seko99/robot/docs/2025-05-10_15-37.png

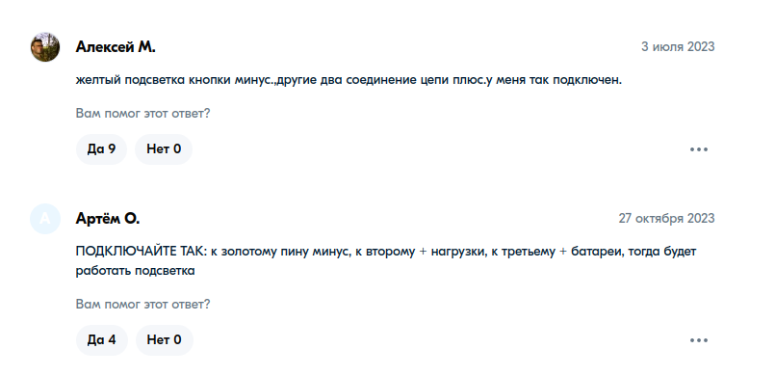
docs/2025-05-10_15-37.png
