seko99/robot/docs/2025-05-10_15-39.png

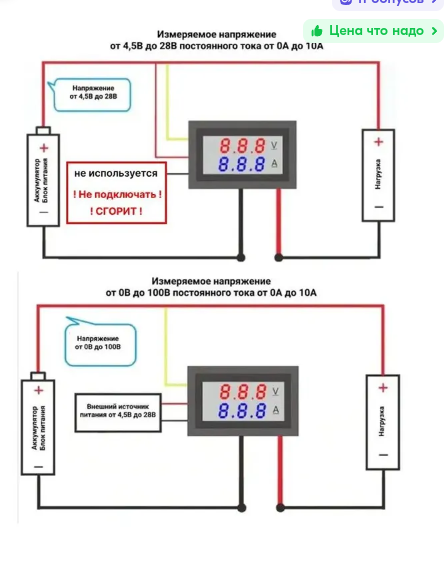
docs/2025-05-10_15-39.png
